Fusion-Lightguns/Fusion-Phaser/DIY/Offical Shell/Print/STLs/Small-STLs/Barrel-Cover-L.stl

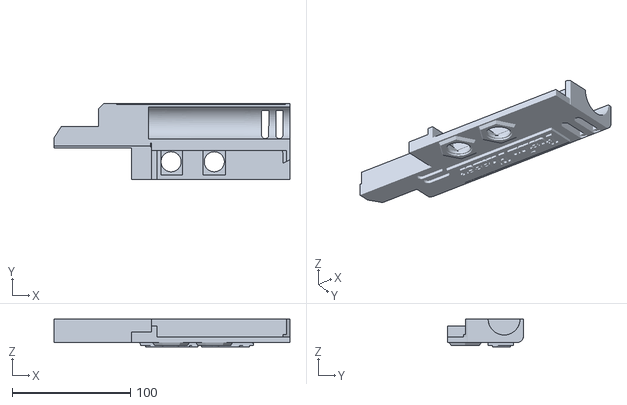
[picture p15: CAD file, 2022-12-12]
DIY/Offical Shell/Print/STLs/Small-STLs/Barrel-Cover-L.stl
200.0 x 64.5 x 23.6
